chrdd/Metal-Detector-Robot/Resources/Robot Arm MK2 Plus/EBAmk2_016_claw_gear_drive.STL

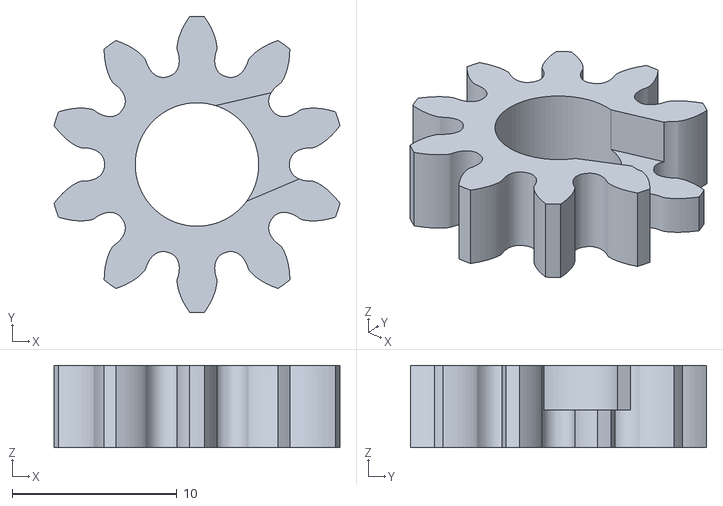
[picture p52: CAD file, 2023-06-09]
Resources/Robot Arm MK2 Plus/EBAmk2_016_claw_gear_drive.STL
17.4 x 18.0 x 5.00
