chrdd/Metal-Detector-Robot/Resources/1204552_3d_print_desktop_robot_arm_DARM_/files/end1.STL

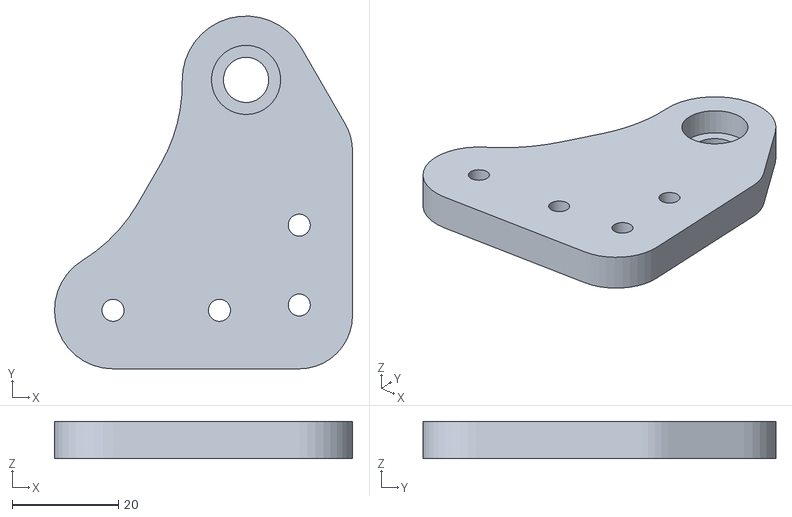
[picture p53: CAD file, 2023-06-09]
Resources/1204552_3d_print_desktop_robot_arm_DARM_/files/end1.STL
56.0 x 66.3 x 7.00
