chrdd/Metal-Detector-Robot/Resources/Arduino Robot Arm STL Files/STL/Arm 01.STL

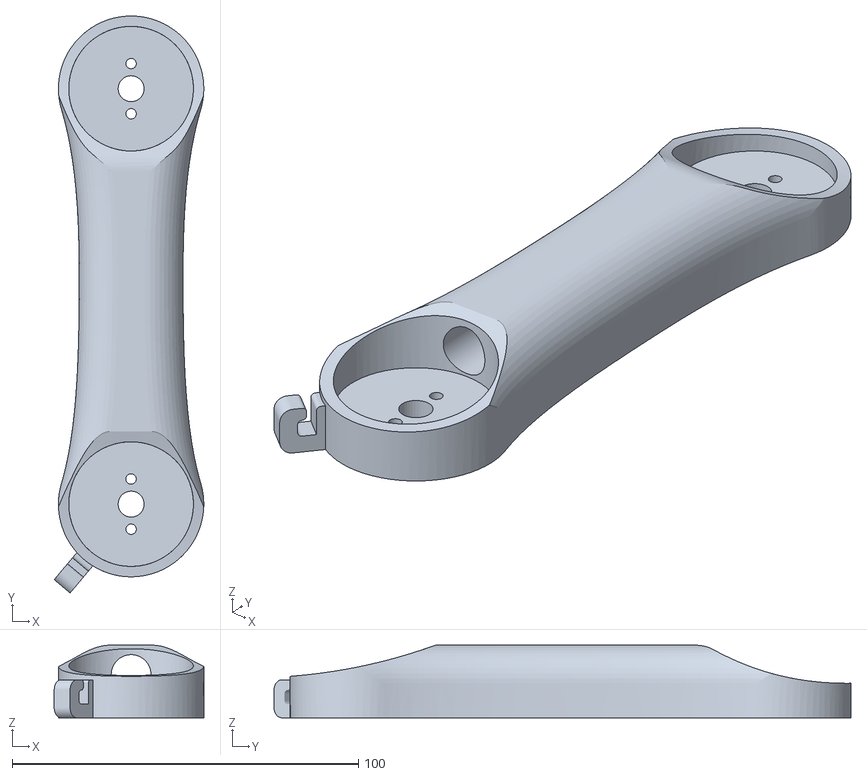
[picture p54: CAD file, 2023-06-09]
Resources/Arduino Robot Arm STL Files/STL/Arm 01.STL
43.2 x 166.7 x 21.0
