chrdd/Metal-Detector-Robot/Resources/Robot Arm MK2 Plus/Base_Bearing_Ball.STL

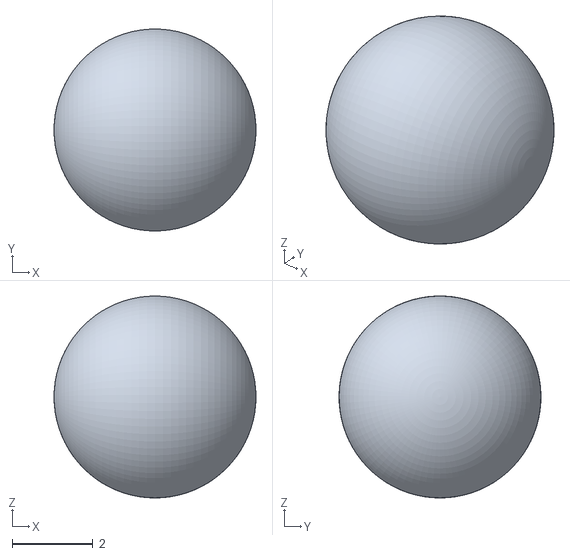
[picture p55: CAD file, 2023-06-09]
Resources/Robot Arm MK2 Plus/Base_Bearing_Ball.STL
5.00 x 5.00 x 5.00
