chrdd/Metal-Detector-Robot/Resources/1204552_3d_print_desktop_robot_arm_DARM_/files/bottomPlate1.STL

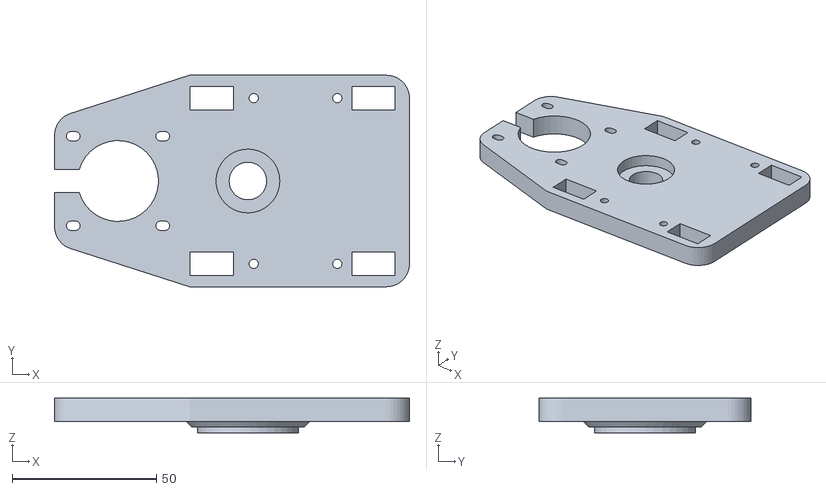
[picture p56: CAD file, 2023-06-09]
Resources/1204552_3d_print_desktop_robot_arm_DARM_/files/bottomPlate1.STL
123.0 x 73.3 x 12.0
