chrdd/Metal-Detector-Robot/Resources/Arduino Robot Arm STL Files/STL/Arm 03.STL

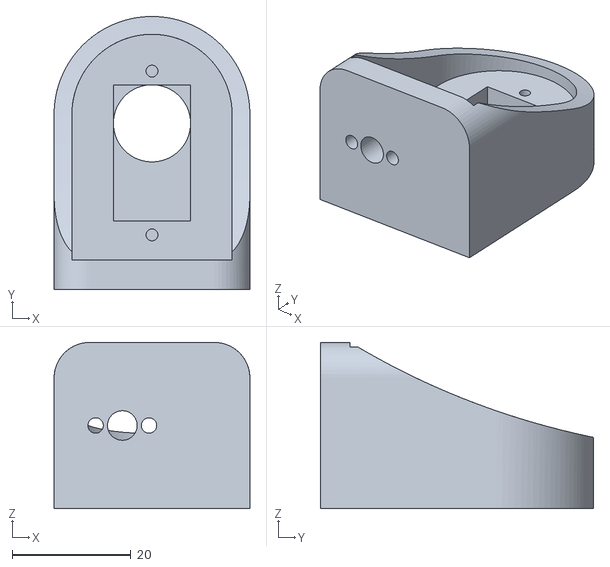
[picture p57: CAD file, 2023-06-09]
Resources/Arduino Robot Arm STL Files/STL/Arm 03.STL
33.0 x 46.0 x 28.0
