chrdd/Metal-Detector-Robot/Resources/Robot Arm MK2 Plus/EBAmk2_014_claw_base.STL

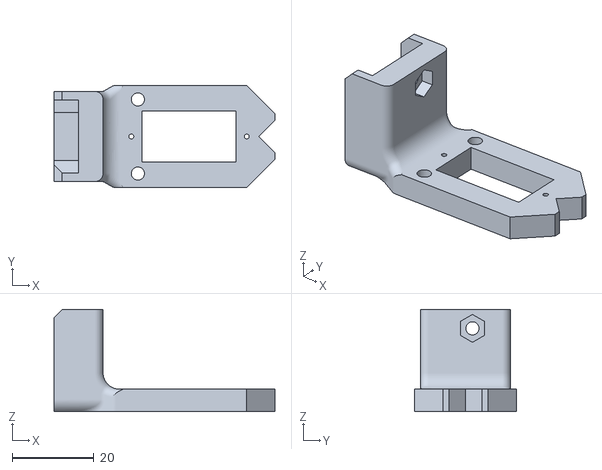
[picture p58: CAD file, 2023-06-09]
Resources/Robot Arm MK2 Plus/EBAmk2_014_claw_base.STL
54.0 x 25.0 x 25.0
