chrdd/Metal-Detector-Robot/Resources/1204552_3d_print_desktop_robot_arm_DARM_/files/690_connect.STL

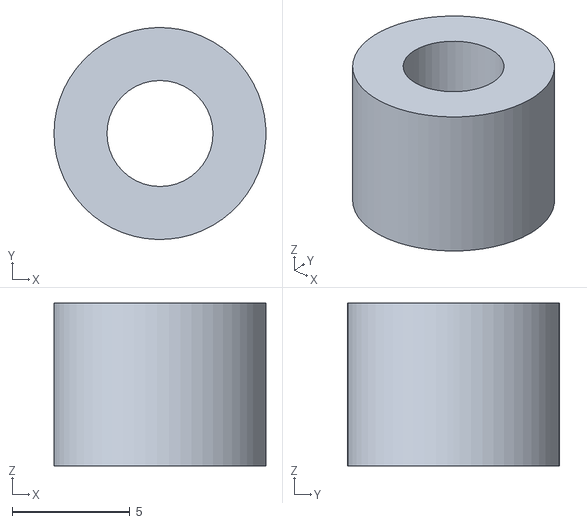
[picture p59: CAD file, 2023-06-09]
Resources/1204552_3d_print_desktop_robot_arm_DARM_/files/690_connect.STL
9.00 x 9.00 x 6.90
