chrdd/Metal-Detector-Robot/Resources/Arduino Robot Arm STL Files/STL/Gripper base.STL

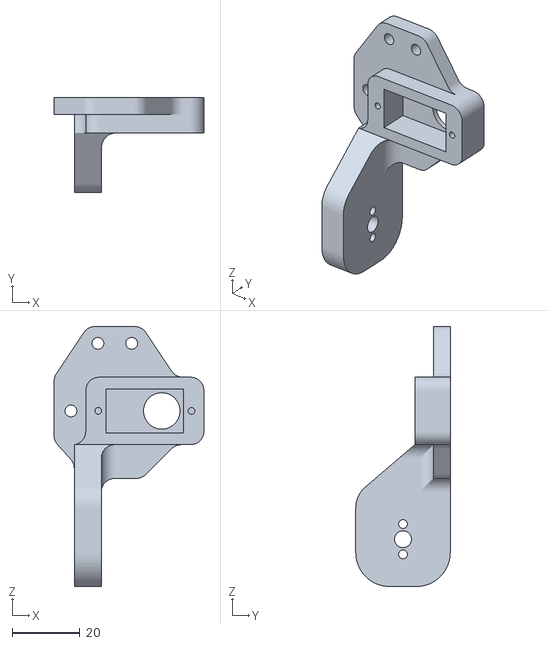
[picture p60: CAD file, 2023-06-09]
Resources/Arduino Robot Arm STL Files/STL/Gripper base.STL
44.4 x 28.0 x 77.0
