chrdd/Metal-Detector-Robot/Resources/Robot Arm MK2 Plus/EBAmk2_004_link135.STL

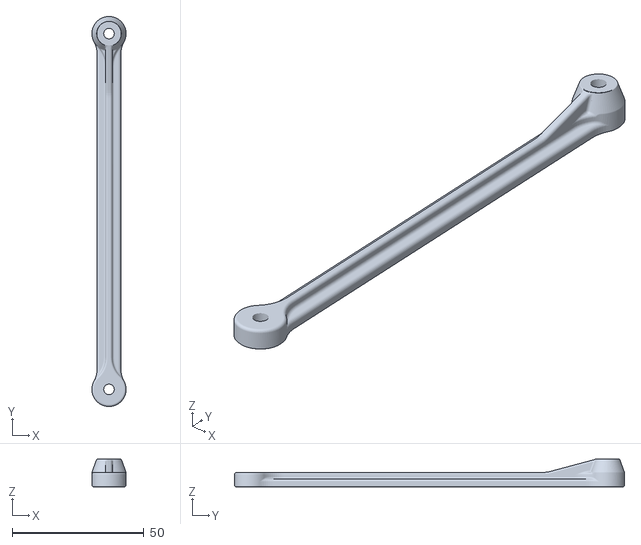
[picture p61: CAD file, 2023-06-09]
Resources/Robot Arm MK2 Plus/EBAmk2_004_link135.STL
13.0 x 148.0 x 10.5
