chrdd/Metal-Detector-Robot/Resources/Arduino Robot Arm STL Files/STL/Arm 02 v3.STL

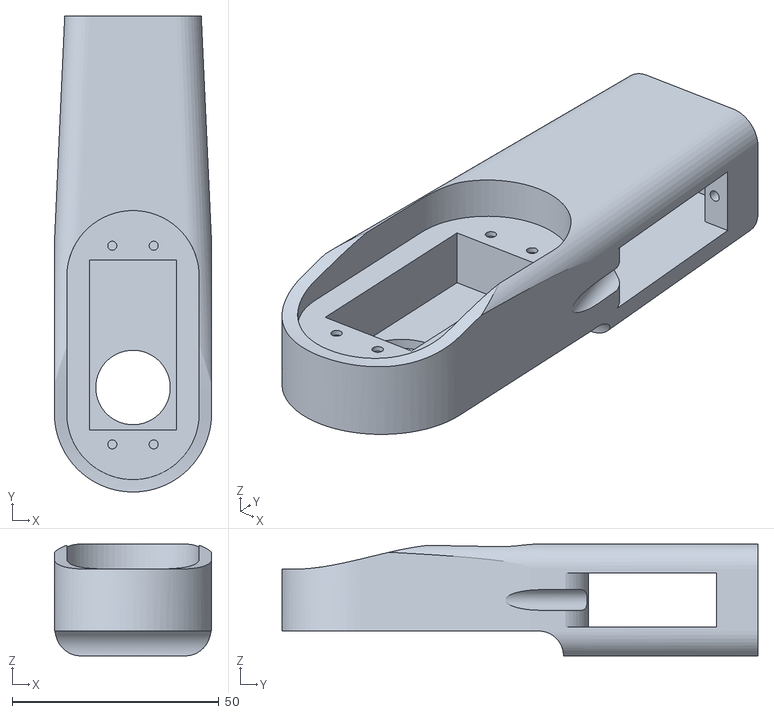
[picture p63: CAD file, 2023-06-09]
Resources/Arduino Robot Arm STL Files/STL/Arm 02 v3.STL
38.0 x 115.0 x 27.0
