chrdd/Metal-Detector-Robot/Resources/Robot Arm MK2 Plus/Base_Bearing_Holder.STL

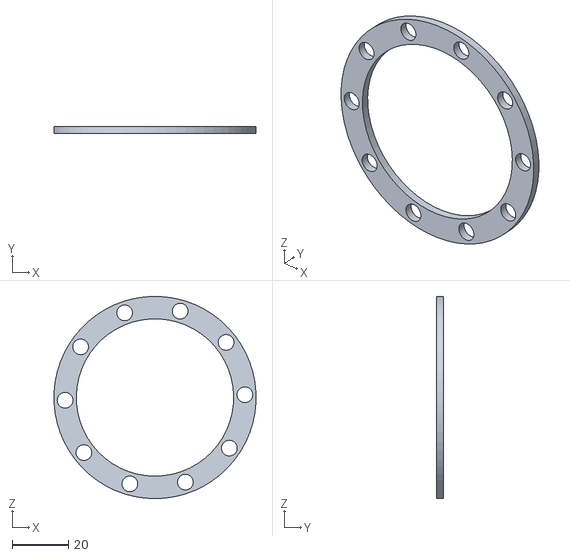
[picture p64: CAD file, 2023-06-09]
Resources/Robot Arm MK2 Plus/Base_Bearing_Holder.STL
71.9 x 2.50 x 72.0
