chrdd/Metal-Detector-Robot/Resources/1204552_3d_print_desktop_robot_arm_DARM_/files/newtriangle.STL

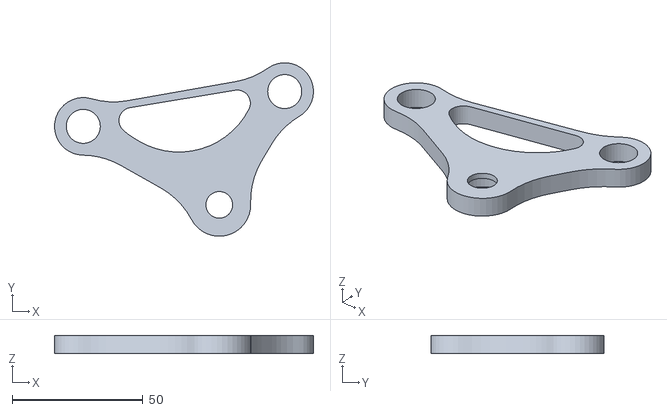
[picture p65: CAD file, 2023-06-09]
Resources/1204552_3d_print_desktop_robot_arm_DARM_/files/newtriangle.STL
99.0 x 66.2 x 7.00
