chrdd/Metal-Detector-Robot/Resources/Arduino Robot Arm STL Files/STL/Base.STL

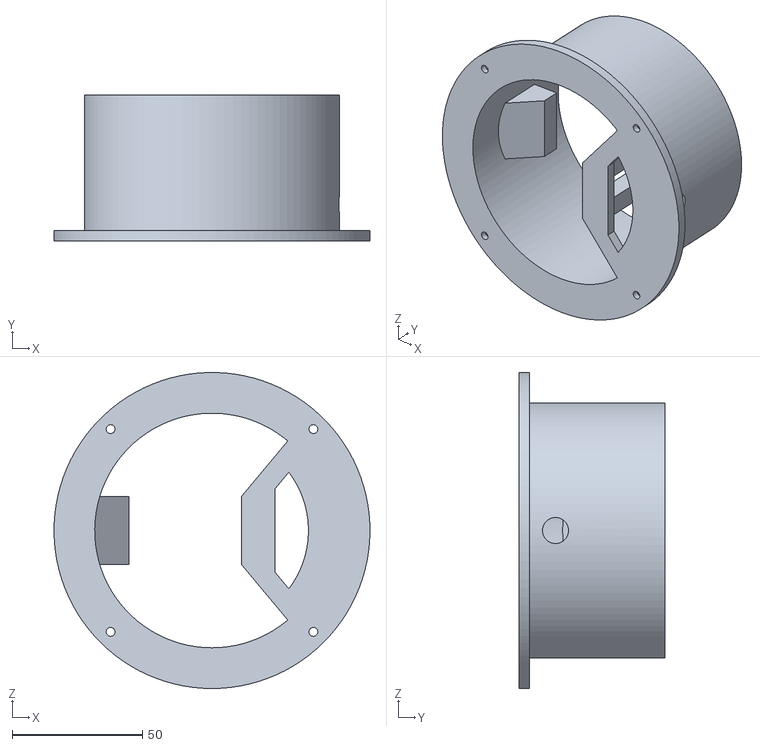
[picture p66: CAD file, 2023-06-09]
Resources/Arduino Robot Arm STL Files/STL/Base.STL
121.2 x 56.0 x 121.2
