chrdd/Metal-Detector-Robot/Resources/Robot Arm MK2 Plus/Stepper_Gear.STL

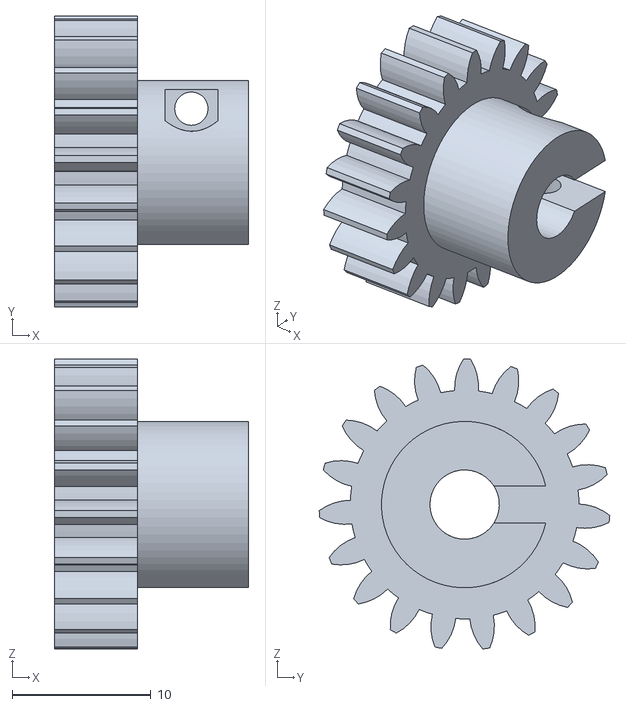
[picture p67: CAD file, 2023-06-09]
Resources/Robot Arm MK2 Plus/Stepper_Gear.STL
14.0 x 21.0 x 20.9
