chrdd/Metal-Detector-Robot/Resources/1204552_3d_print_desktop_robot_arm_DARM_/files/bottomPlate2.STL

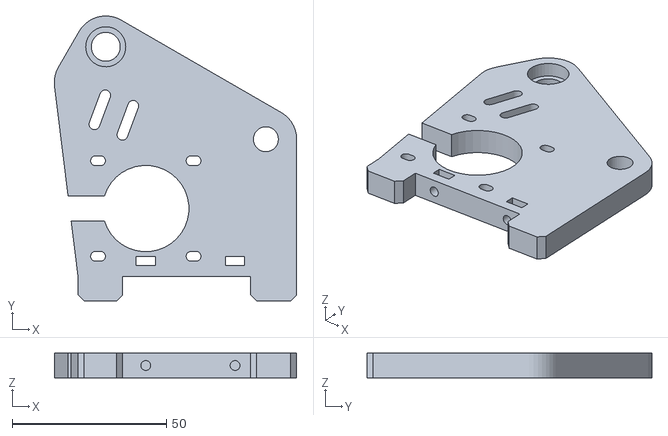
[picture p68: CAD file, 2023-06-09]
Resources/1204552_3d_print_desktop_robot_arm_DARM_/files/bottomPlate2.STL
78.7 x 92.5 x 8.00
