chrdd/Metal-Detector-Robot/Resources/Arduino Robot Arm STL Files/STL/grip link 1.STL

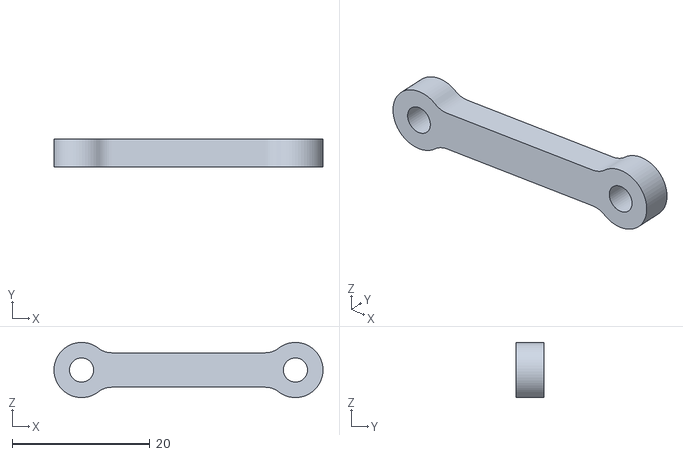
[picture p69: CAD file, 2023-06-09]
Resources/Arduino Robot Arm STL Files/STL/grip link 1.STL
39.0 x 4.00 x 8.00
