chrdd/Metal-Detector-Robot/Resources/Robot Arm MK2 Plus/EBAmk2_017_claw_finger_sx.STL

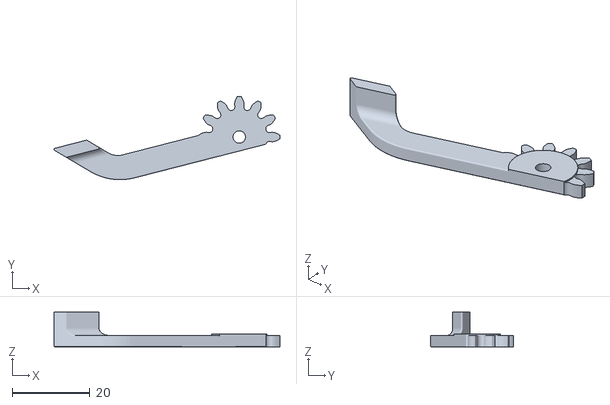
[picture p70: CAD file, 2023-06-09]
Resources/Robot Arm MK2 Plus/EBAmk2_017_claw_finger_sx.STL
58.3 x 21.5 x 9.00
