chrdd/Metal-Detector-Robot/Resources/1204552_3d_print_desktop_robot_arm_DARM_/files/secondEndstop.STL

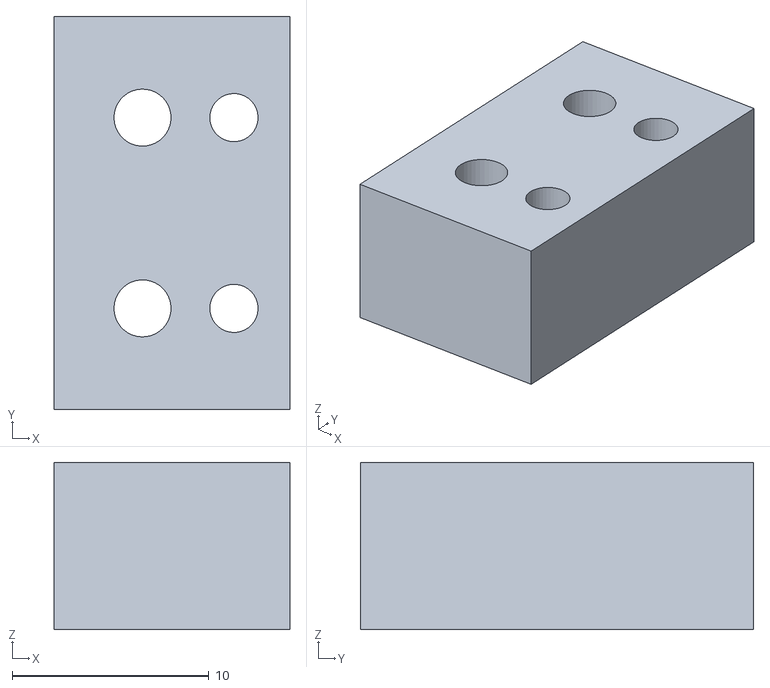
[picture p71: CAD file, 2023-06-09]
Resources/1204552_3d_print_desktop_robot_arm_DARM_/files/secondEndstop.STL
12.0 x 20.0 x 8.50
