chrdd/Metal-Detector-Robot/Resources/Robot Arm MK2 Plus/Robot_Base_Low.STL

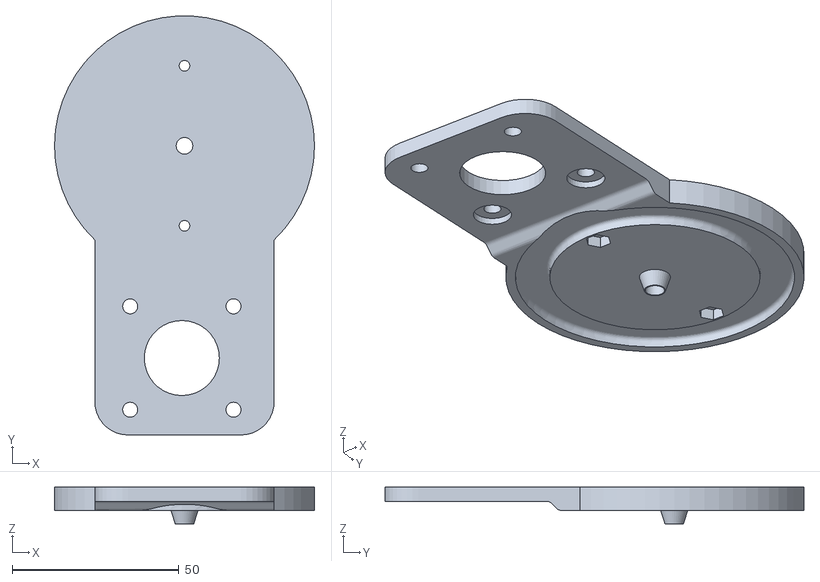
[picture p72: CAD file, 2023-06-09]
Resources/Robot Arm MK2 Plus/Robot_Base_Low.STL
78.0 x 125.7 x 11.0
