chrdd/Metal-Detector-Robot/Resources/Robot Arm MK2 Plus/gear1.STL

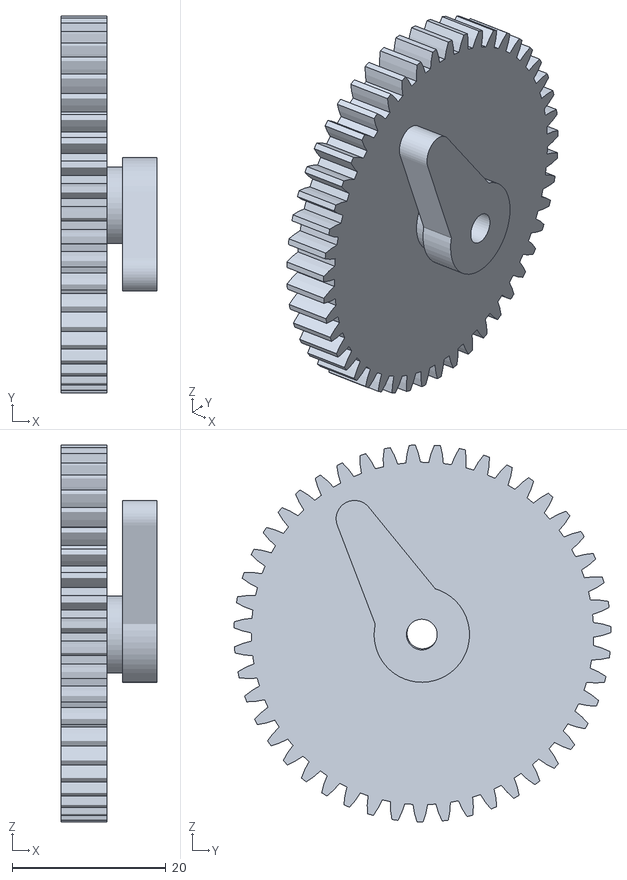
[picture p73: CAD file, 2023-06-09]
Resources/Robot Arm MK2 Plus/gear1.STL
12.5 x 49.0 x 49.0
