chrdd/Metal-Detector-Robot/Resources/1204552_3d_print_desktop_robot_arm_DARM_/files/arm2_corner1.STL

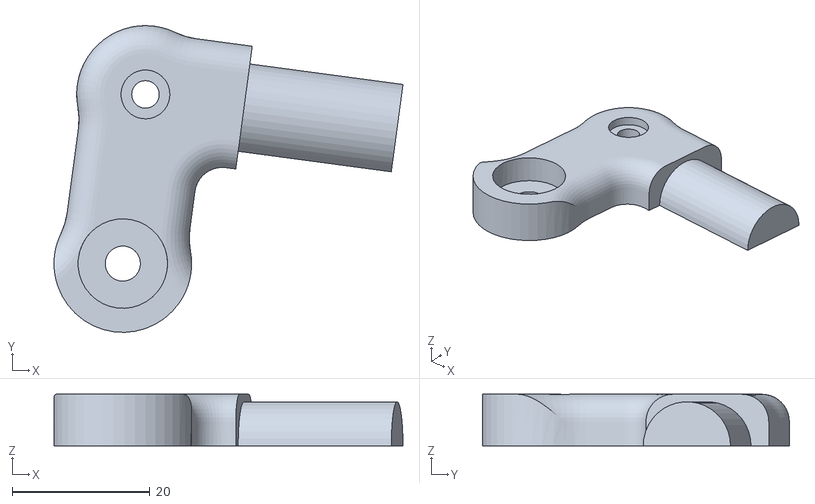
[picture p74: CAD file, 2023-06-09]
Resources/1204552_3d_print_desktop_robot_arm_DARM_/files/arm2_corner1.STL
50.7 x 44.6 x 7.50
