chrdd/Metal-Detector-Robot/Resources/1204552_3d_print_desktop_robot_arm_DARM_/files/arm2_end.STL

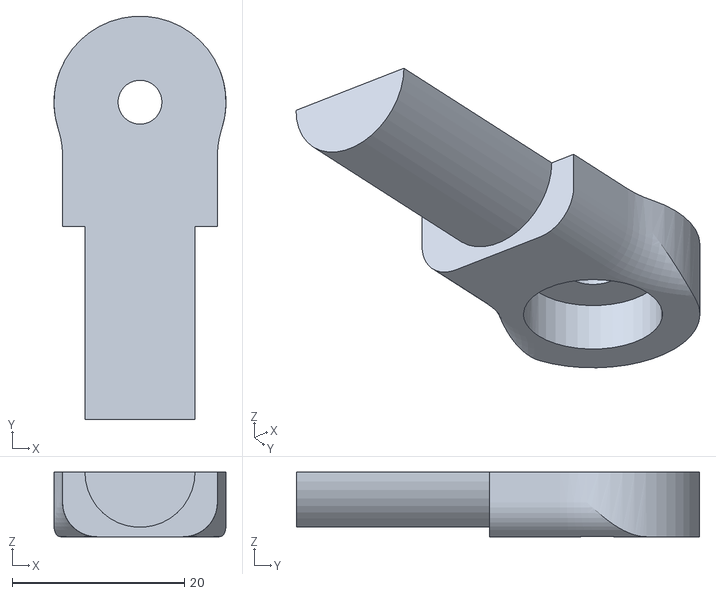
[picture p75: CAD file, 2023-06-09]
Resources/1204552_3d_print_desktop_robot_arm_DARM_/files/arm2_end.STL
20.0 x 46.9 x 7.50
