chrdd/Metal-Detector-Robot/Resources/1204552_3d_print_desktop_robot_arm_DARM_/files/Pen_clip.STL

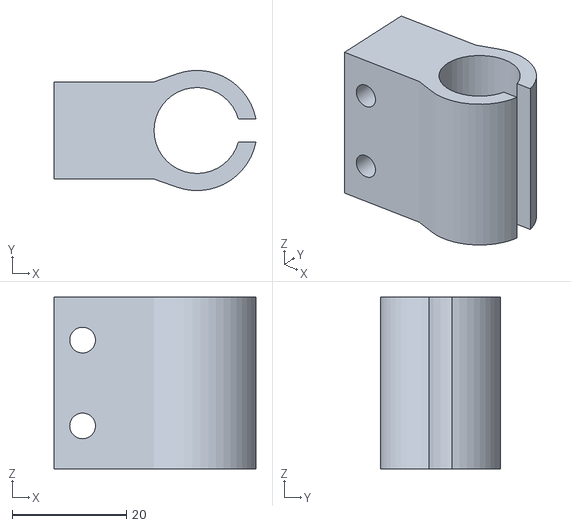
[picture p76: CAD file, 2023-06-09]
Resources/1204552_3d_print_desktop_robot_arm_DARM_/files/Pen_clip.STL
35.3 x 21.0 x 30.0
