chrdd/Metal-Detector-Robot/Resources/Robot Arm MK2 Plus/EBAmk2_015_claw_finger_dx.STL

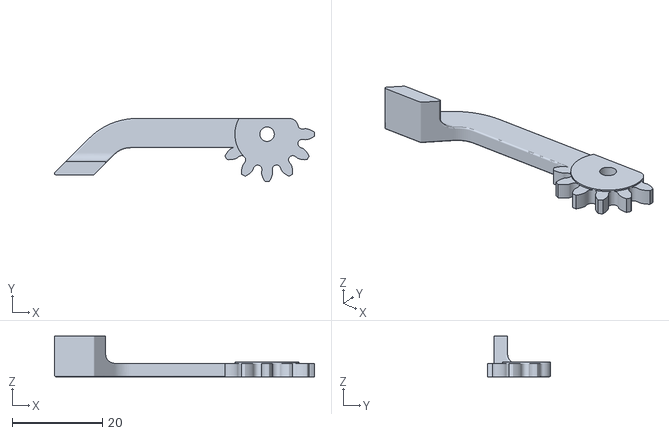
[picture p77: CAD file, 2023-06-09]
Resources/Robot Arm MK2 Plus/EBAmk2_015_claw_finger_dx.STL
57.6 x 14.0 x 9.00
