chrdd/Metal-Detector-Robot/Resources/1204552_3d_print_desktop_robot_arm_DARM_/files/bottomPlate3.STL

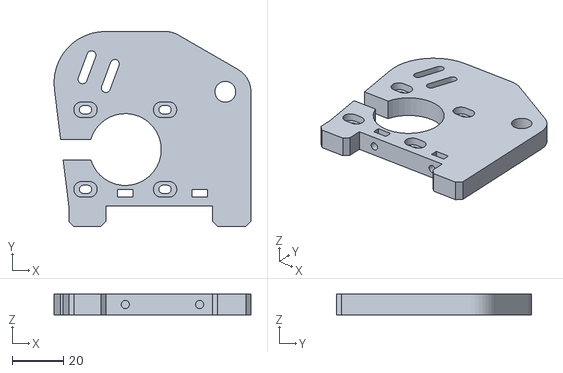
[picture p78: CAD file, 2023-06-09]
Resources/1204552_3d_print_desktop_robot_arm_DARM_/files/bottomPlate3.STL
76.7 x 76.0 x 8.00
