chrdd/Metal-Detector-Robot/Resources/Robot Arm MK2 Plus/Robot_Base_Low_Gear.STL

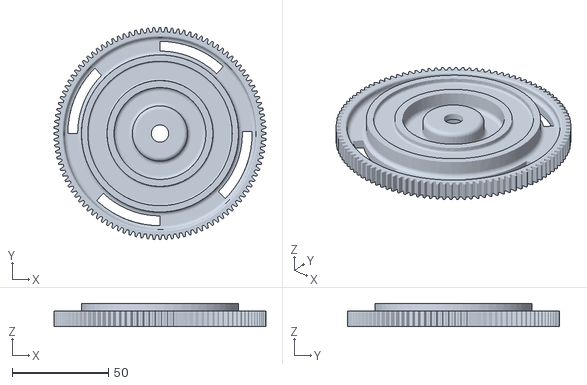
[picture p79: CAD file, 2023-06-09]
Resources/Robot Arm MK2 Plus/Robot_Base_Low_Gear.STL
110.0 x 110.0 x 12.0
