chrdd/Metal-Detector-Robot/Resources/Robot Arm MK2 Plus/EBAmk2_006_horarm__.STL

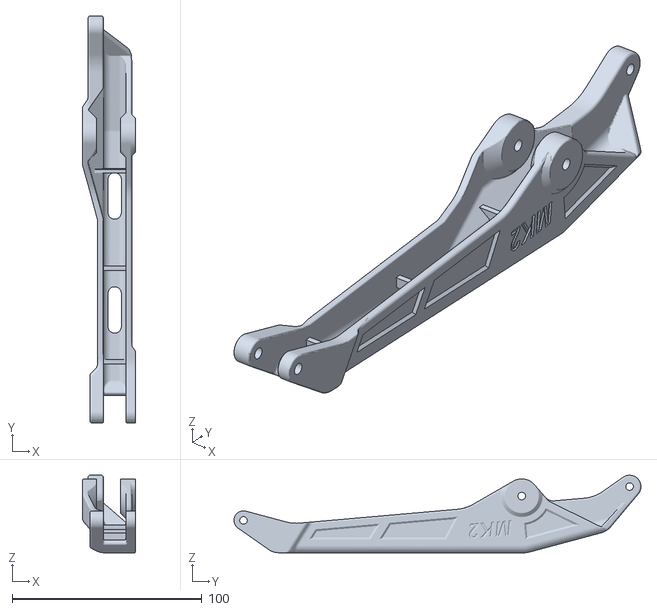
[picture p80: CAD file, 2023-06-09]
Resources/Robot Arm MK2 Plus/EBAmk2_006_horarm__.STL
28.0 x 214.2 x 40.9
