chrdd/Metal-Detector-Robot/Resources/1204552_3d_print_desktop_robot_arm_DARM_/files/8MMLock.STL

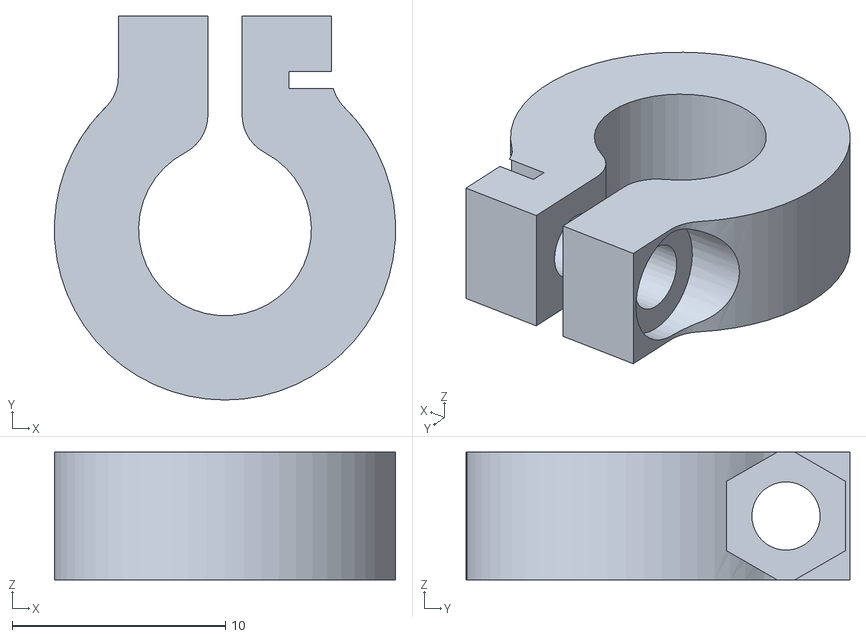
[picture p81: CAD file, 2023-06-09]
Resources/1204552_3d_print_desktop_robot_arm_DARM_/files/8MMLock.STL
16.0 x 18.0 x 6.00
