chrdd/Metal-Detector-Robot/Resources/Robot Arm MK2 Plus/EBAmk2_008_link147_new.STL

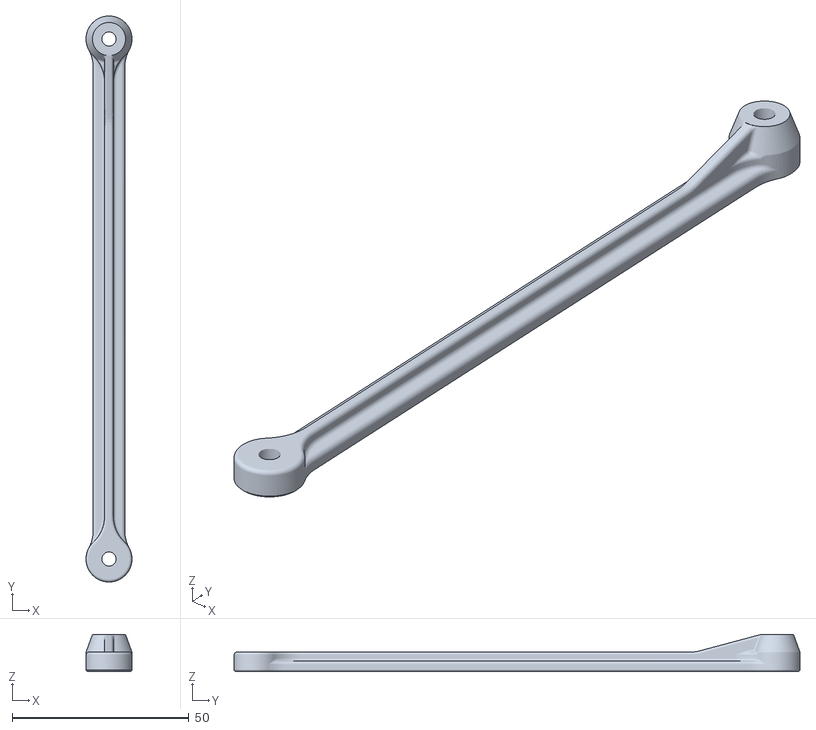
[picture p82: CAD file, 2023-06-09]
Resources/Robot Arm MK2 Plus/EBAmk2_008_link147_new.STL
13.0 x 160.0 x 10.5
