chrdd/Metal-Detector-Robot/Resources/1204552_3d_print_desktop_robot_arm_DARM_/files/15mm_bracket.STL

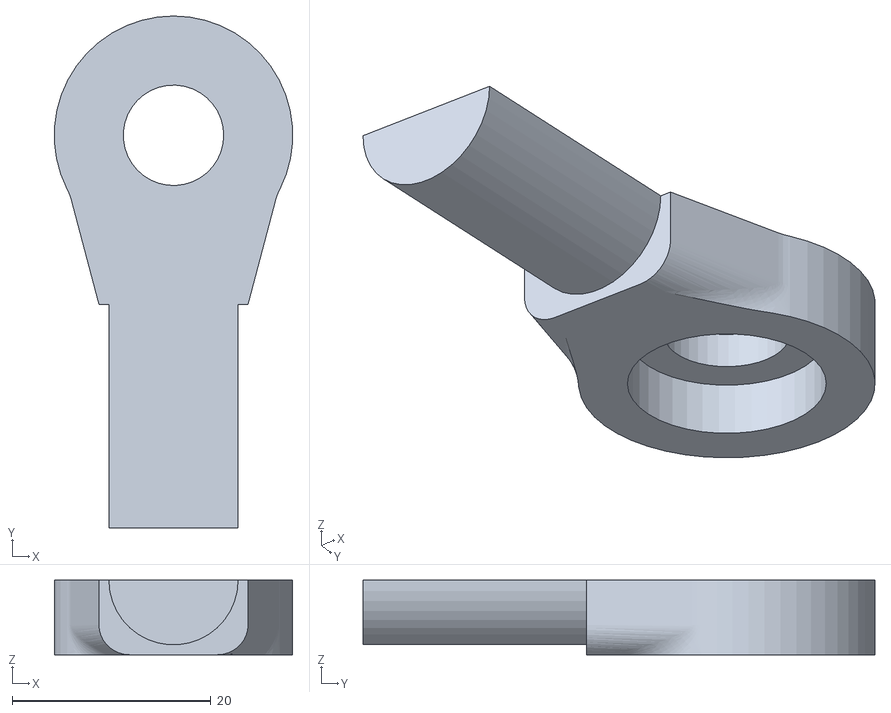
[picture p83: CAD file, 2023-06-09]
Resources/1204552_3d_print_desktop_robot_arm_DARM_/files/15mm_bracket.STL
24.0 x 51.5 x 7.50
