chrdd/Metal-Detector-Robot/Resources/Robot Arm MK2 Plus/EBAmk2_018_claw_gear_driven.STL

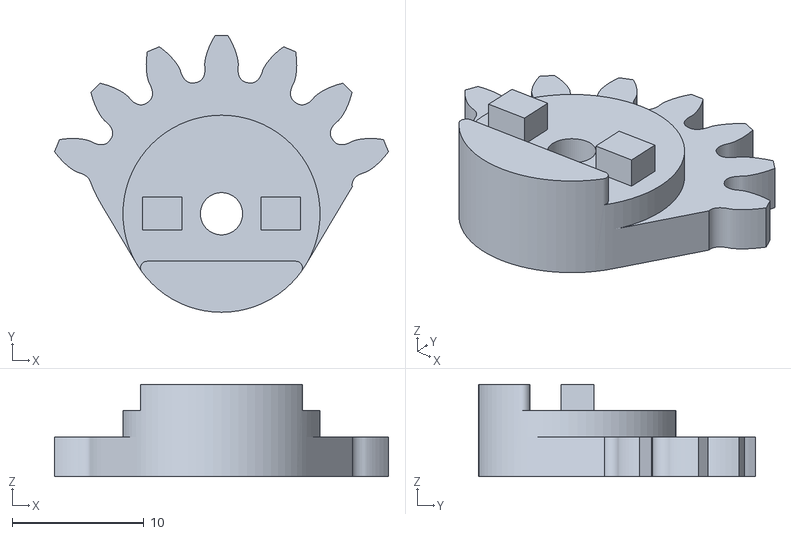
[picture p84: CAD file, 2023-06-09]
Resources/Robot Arm MK2 Plus/EBAmk2_018_claw_gear_driven.STL
25.3 x 21.0 x 7.00
