chrdd/Metal-Detector-Robot/Resources/1204552_3d_print_desktop_robot_arm_DARM_/files/secondArmGear685.STL

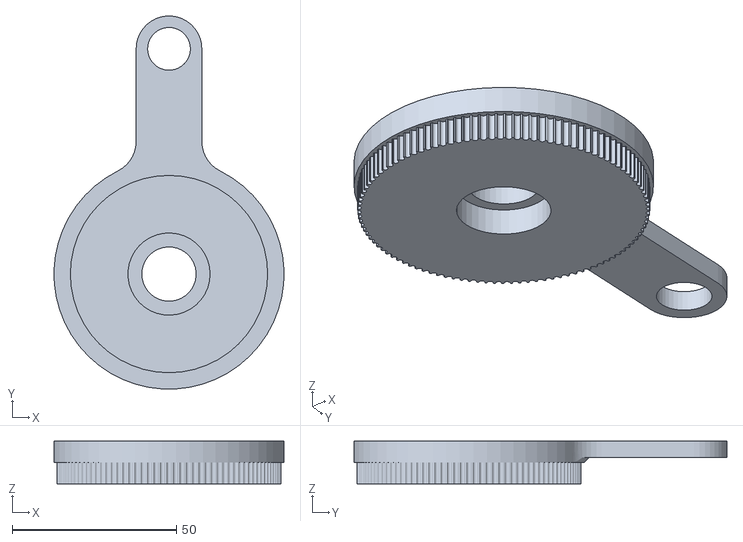
[picture p85: CAD file, 2023-06-09]
Resources/1204552_3d_print_desktop_robot_arm_DARM_/files/secondArmGear685.STL
69.9 x 113.4 x 13.0
