chrdd/Metal-Detector-Robot/Resources/Robot Arm MK2 Plus/EBAmk2_007_trialink.STL

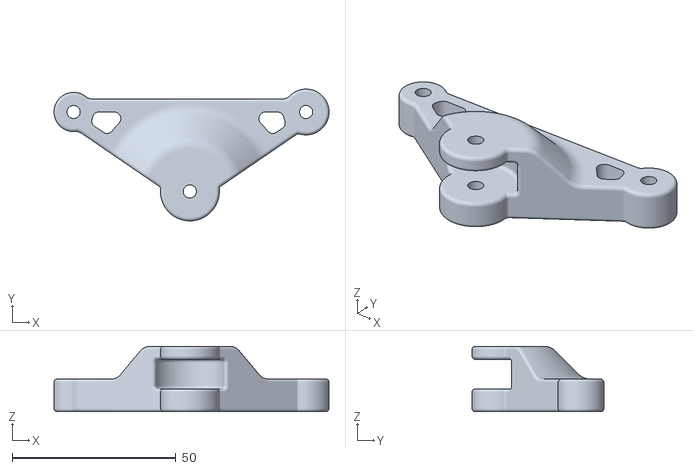
[picture p86: CAD file, 2023-06-09]
Resources/Robot Arm MK2 Plus/EBAmk2_007_trialink.STL
84.0 x 40.3 x 20.0
