chrdd/Metal-Detector-Robot/Resources/1204552_3d_print_desktop_robot_arm_DARM_/files/Gears_bottom.STL

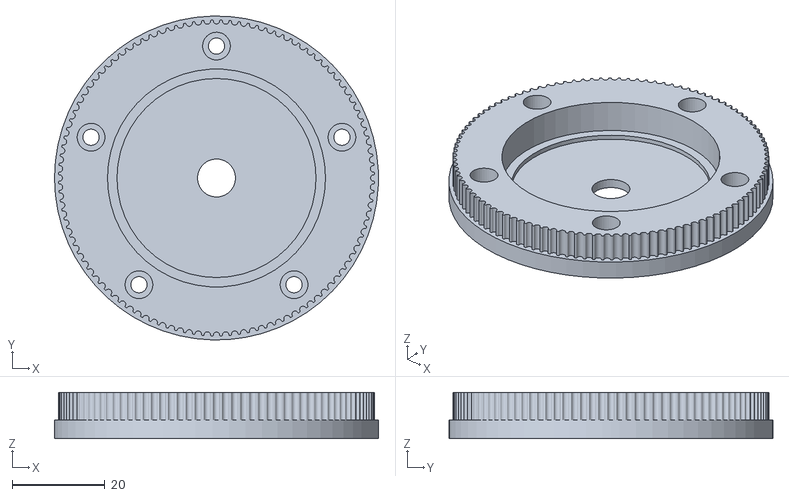
[picture p87: CAD file, 2023-06-09]
Resources/1204552_3d_print_desktop_robot_arm_DARM_/files/Gears_bottom.STL
70.0 x 70.0 x 10.0
