chrdd/Metal-Detector-Robot/Resources/Robot Arm MK2 Plus/EBAmk2_003_varm.STL

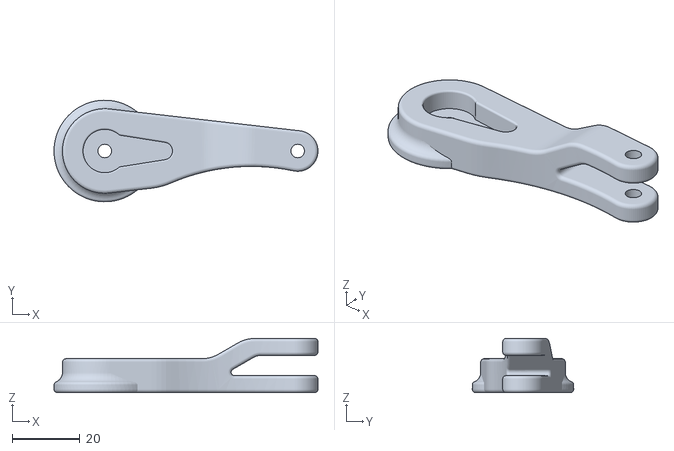
[picture p88: CAD file, 2023-06-09]
Resources/Robot Arm MK2 Plus/EBAmk2_003_varm.STL
78.0 x 30.0 x 16.0
