chrdd/Metal-Detector-Robot/Resources/Robot Arm MK2 Plus/EBAmk2_006_horarm_plate.STL

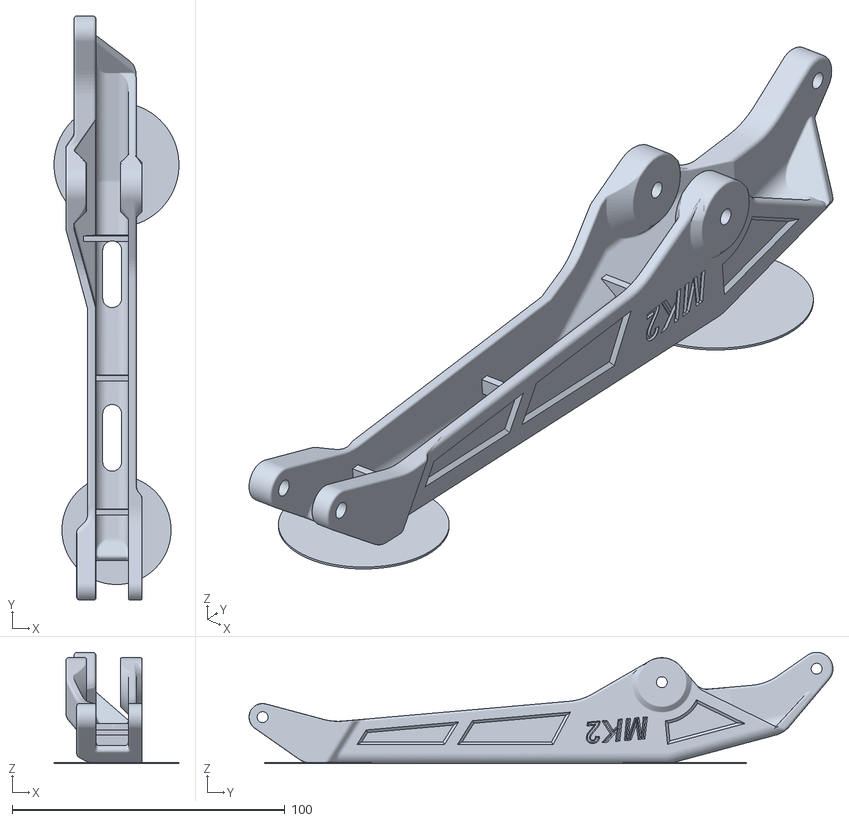
[picture p89: CAD file, 2023-06-09]
Resources/Robot Arm MK2 Plus/EBAmk2_006_horarm_plate.STL
45.8 x 214.2 x 40.9
