chrdd/Metal-Detector-Robot/Resources/1204552_3d_print_desktop_robot_arm_DARM_/files/15mm_bracket_2.STL

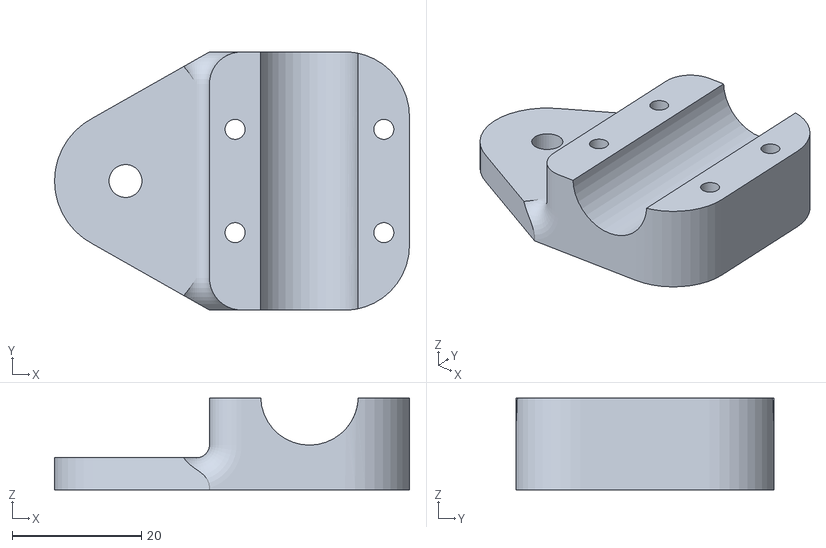
[picture p90: CAD file, 2023-06-09]
Resources/1204552_3d_print_desktop_robot_arm_DARM_/files/15mm_bracket_2.STL
55.0 x 40.0 x 14.3
