chrdd/Metal-Detector-Robot/Resources/Robot Arm MK2 Plus/gear2.STL

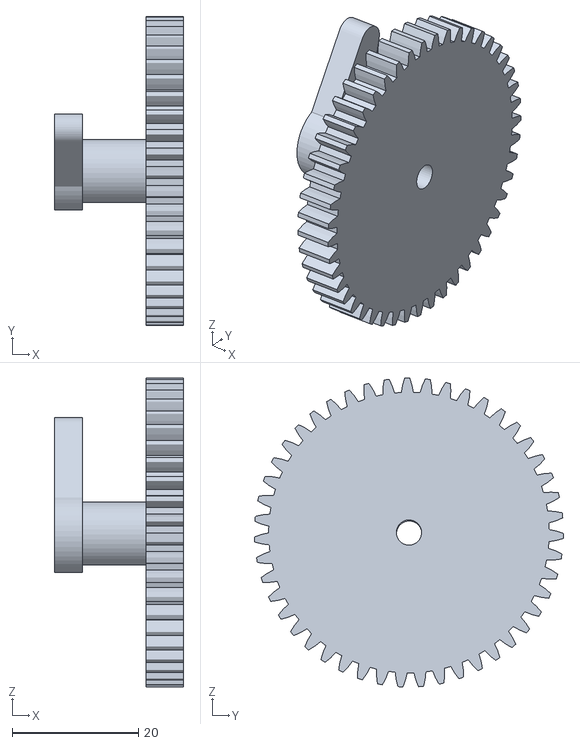
[picture p91: CAD file, 2023-06-09]
Resources/Robot Arm MK2 Plus/gear2.STL
20.5 x 49.0 x 49.0
