chrdd/Metal-Detector-Robot/Resources/1204552_3d_print_desktop_robot_arm_DARM_/files/rod_ends.STL

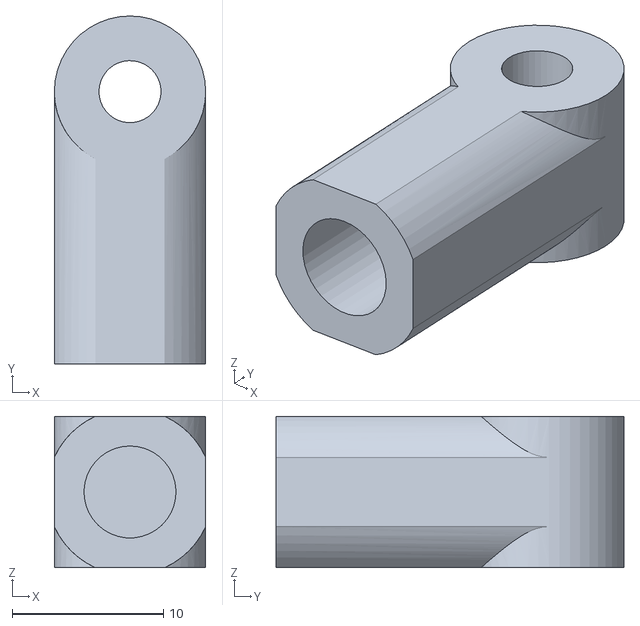
[picture p92: CAD file, 2023-06-09]
Resources/1204552_3d_print_desktop_robot_arm_DARM_/files/rod_ends.STL
10.0 x 23.0 x 10.00
