chrdd/Metal-Detector-Robot/Resources/1204552_3d_print_desktop_robot_arm_DARM_/files/675_cennect.STL

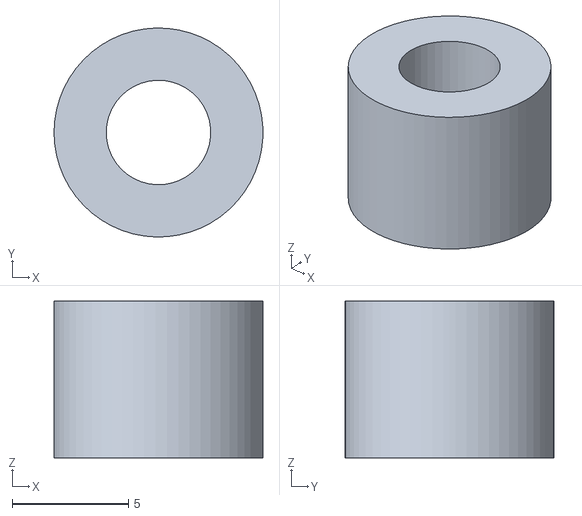
[picture p93: CAD file, 2023-06-09]
Resources/1204552_3d_print_desktop_robot_arm_DARM_/files/675_cennect.STL
9.00 x 9.00 x 6.75
