chrdd/Metal-Detector-Robot/Resources/Robot Arm MK2 Plus/EBAmk2_005_link135angled.STL

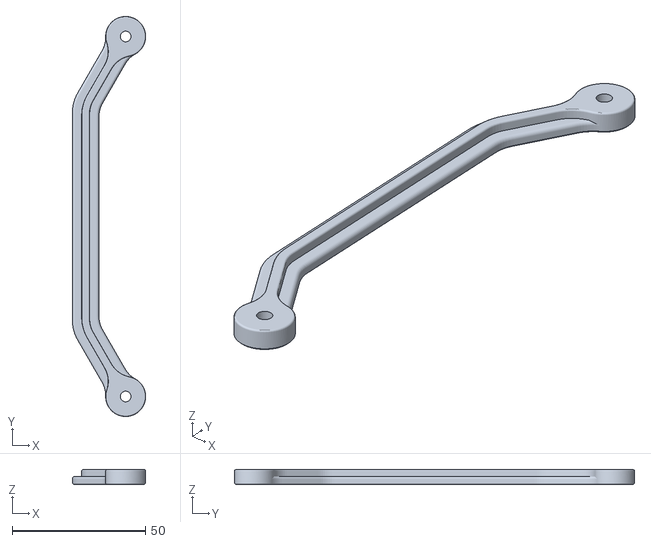
[picture p94: CAD file, 2023-06-09]
Resources/Robot Arm MK2 Plus/EBAmk2_005_link135angled.STL
27.5 x 150.0 x 5.50
