chrdd/Metal-Detector-Robot/Resources/1204552_3d_print_desktop_robot_arm_DARM_/files/bottomPlate.STL

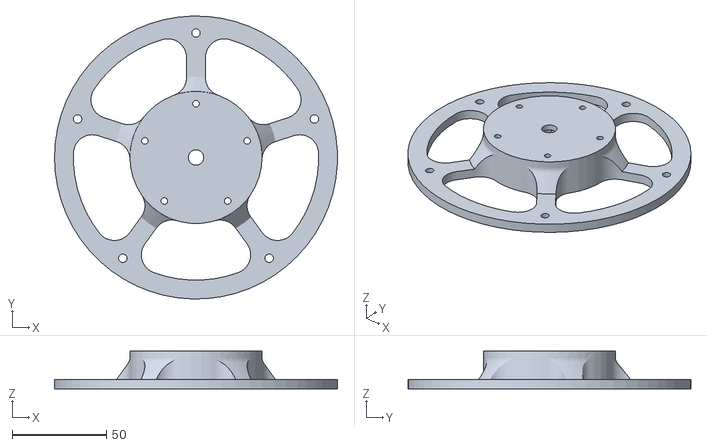
[picture p95: CAD file, 2023-06-09]
Resources/1204552_3d_print_desktop_robot_arm_DARM_/files/bottomPlate.STL
150.0 x 150.0 x 20.0
